mikegoelzer/Homebrew-ECP5-SBC/hardware/parts/GRM1885C1H121JA01D/G-188_MUR.step

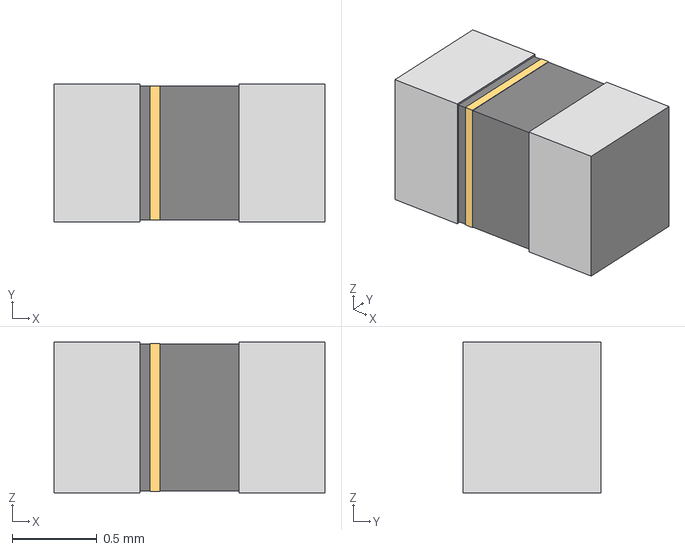
[picture p17: CAD file, 2024-12-17]
hardware/parts/GRM1885C1H121JA01D/G-188_MUR.step
1.60 x 0.812 x 0.889 mm
