mikegoelzer/Homebrew-ECP5-SBC/hardware/parts/ICD15S13E4GX00LF/ICD15S13E4GX00LF.step

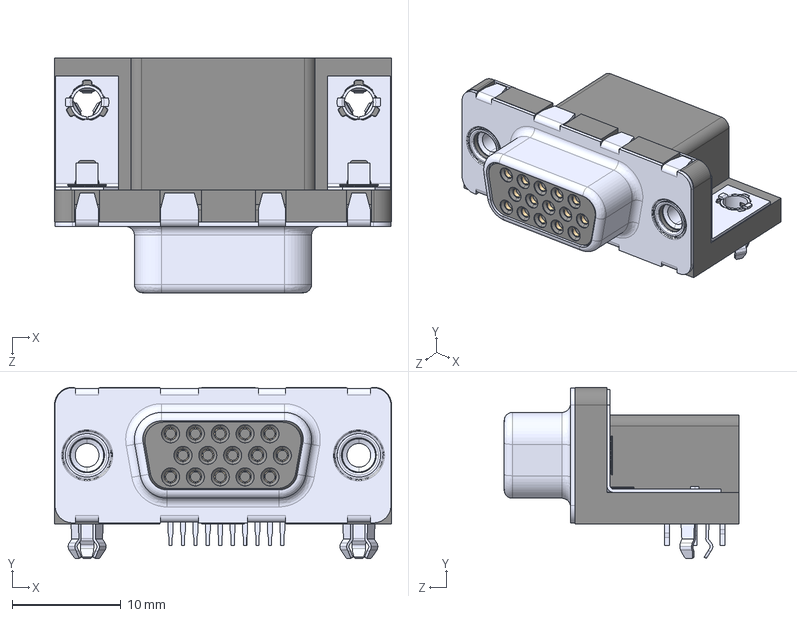
[picture p18: CAD file, 2025-01-06]
hardware/parts/ICD15S13E4GX00LF/ICD15S13E4GX00LF.step
31.0 x 15.7 x 21.6 mm
