mikegoelzer/Homebrew-ECP5-SBC/hardware/parts/IHLP1212ABERR47M11/IND_IHLP-1212AB_VIS.step

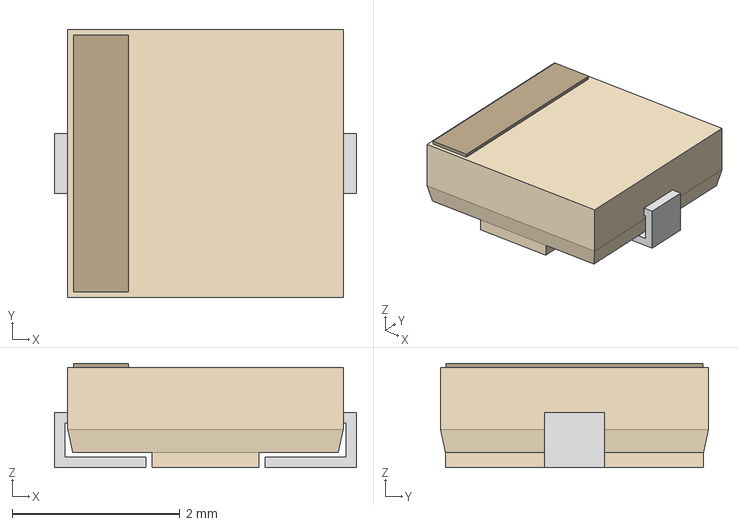
[picture p19: CAD file, 2024-12-17]
hardware/parts/IHLP1212ABERR47M11/IND_IHLP-1212AB_VIS.step
3.61 x 3.20 x 1.25 mm
