mikegoelzer/Homebrew-ECP5-SBC/hardware/parts/IHLP1212AEERR47M11/IND_IHLP-1212AE_VIS.step

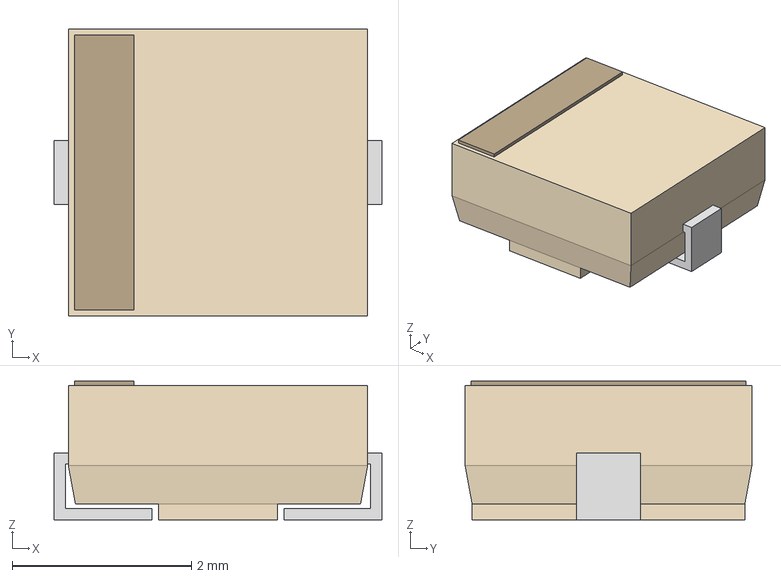
[picture p20: CAD file, 2024-12-17]
hardware/parts/IHLP1212AEERR47M11/IND_IHLP-1212AE_VIS.step
3.66 x 3.20 x 1.55 mm
