mikegoelzer/Homebrew-ECP5-SBC/hardware/parts/IHLP3232DZER2R2M11/IHLP3232DZ.step

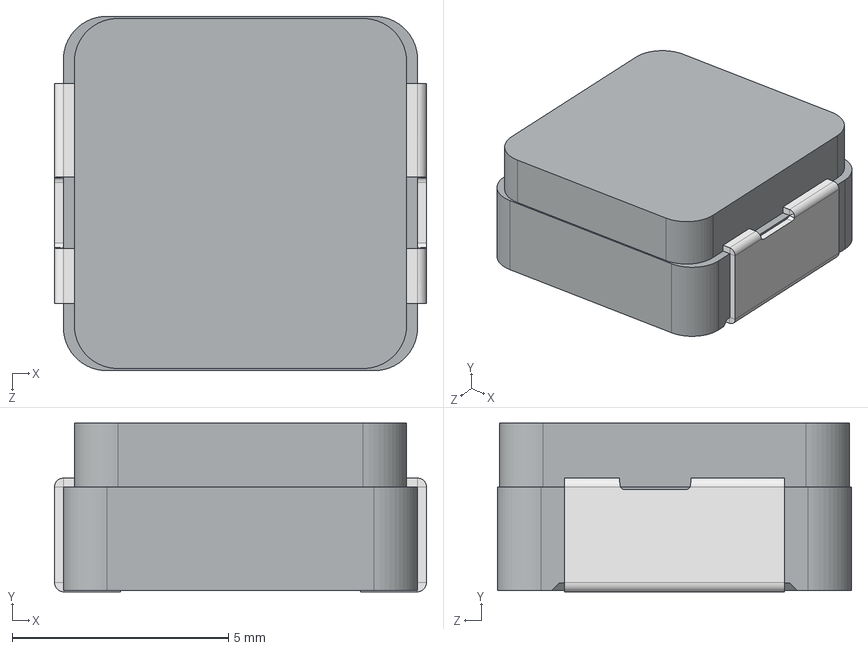
[picture p21: CAD file, 2024-12-17]
hardware/parts/IHLP3232DZER2R2M11/IHLP3232DZ.step
8.60 x 3.90 x 8.19 mm
