mikegoelzer/Homebrew-ECP5-SBC/hardware/parts/IHLP6767DZER6R8M11/IHLP6767DZ.step

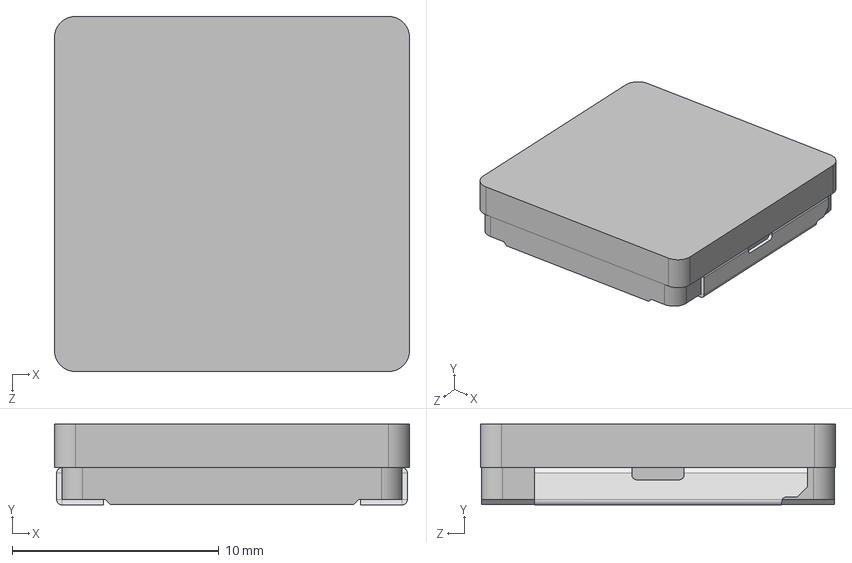
[picture p22: CAD file, 2025-01-10]
hardware/parts/IHLP6767DZER6R8M11/IHLP6767DZ.step
17.2 x 3.91 x 17.2 mm
