mikegoelzer/Homebrew-ECP5-SBC/hardware/parts/INA210BIDCKR/INA210BIDCKR.step

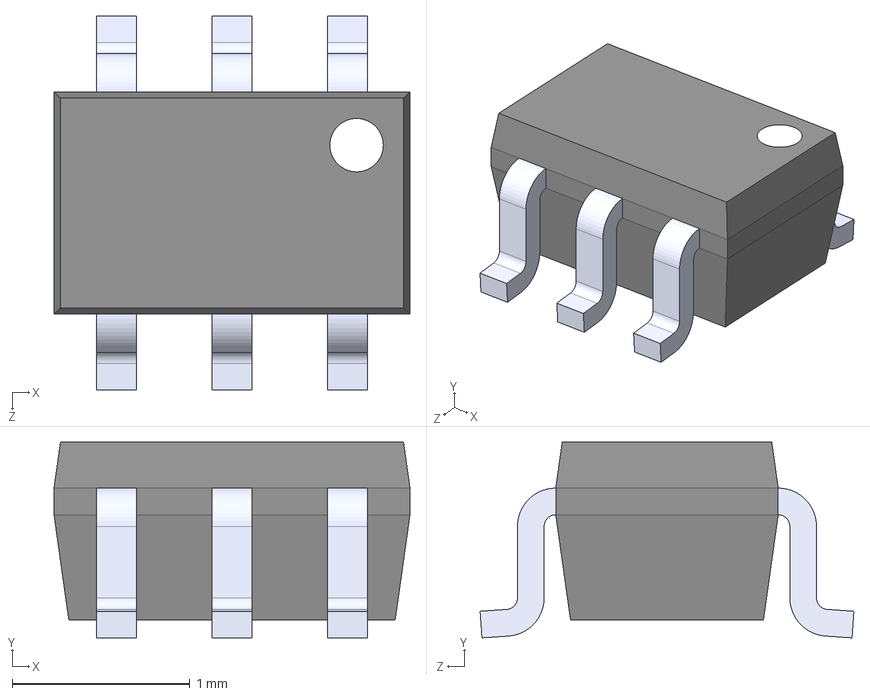
[picture p23: CAD file, 2024-12-17]
hardware/parts/INA210BIDCKR/INA210BIDCKR.step
2.00 x 1.10 x 2.10 mm
