mikegoelzer/Homebrew-ECP5-SBC/hardware/parts/IRF9540NSTRLPBF/IRF9540NSTRLPBF.step

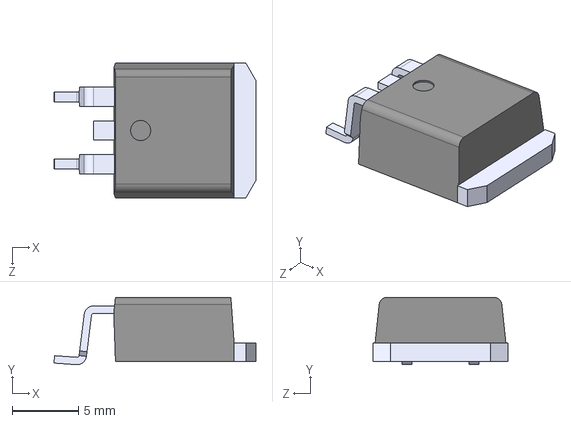
[picture p24: CAD file, 2024-12-17]
hardware/parts/IRF9540NSTRLPBF/IRF9540NSTRLPBF.step
15.2 x 5.08 x 10.2 mm
