mikegoelzer/Homebrew-ECP5-SBC/hardware/parts/Keystone_Testpoints/TestPointKeystone5002WHITE.step

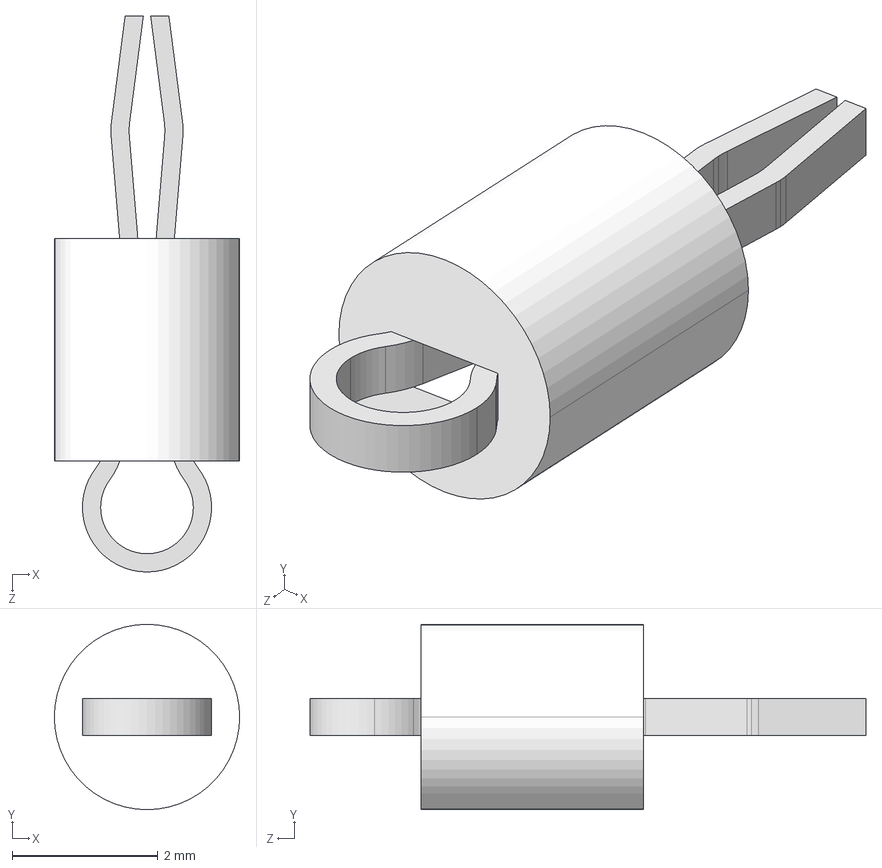
[picture p25: CAD file, 2025-01-06]
hardware/parts/Keystone_Testpoints/TestPointKeystone5002WHITE.step
2.54 x 2.54 x 7.62 mm
User Library-Test Point Keystone - 5002 WHITE_1
User Library-Test Point Keystone - 5002 WHITE_2
