mikegoelzer/Homebrew-ECP5-SBC/hardware/parts/LP2950CDTX_3_3_NOPB/NDP0003B.stp

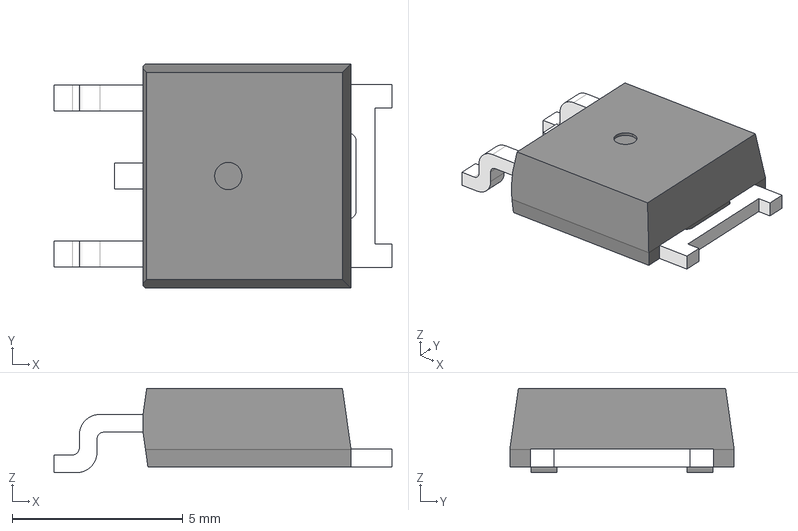
[picture p26: CAD file, 2025-01-10]
hardware/parts/LP2950CDTX_3_3_NOPB/NDP0003B.stp
9.91 x 6.58 x 2.47 mm
BODY_NDP0003B
HSINK_NDP0003B
LEAD_NDP0003B x 2
CLEAD_NDP0003B
