mikegoelzer/Homebrew-ECP5-SBC/hardware/parts/MSD_4_A/MSD-4-A.step

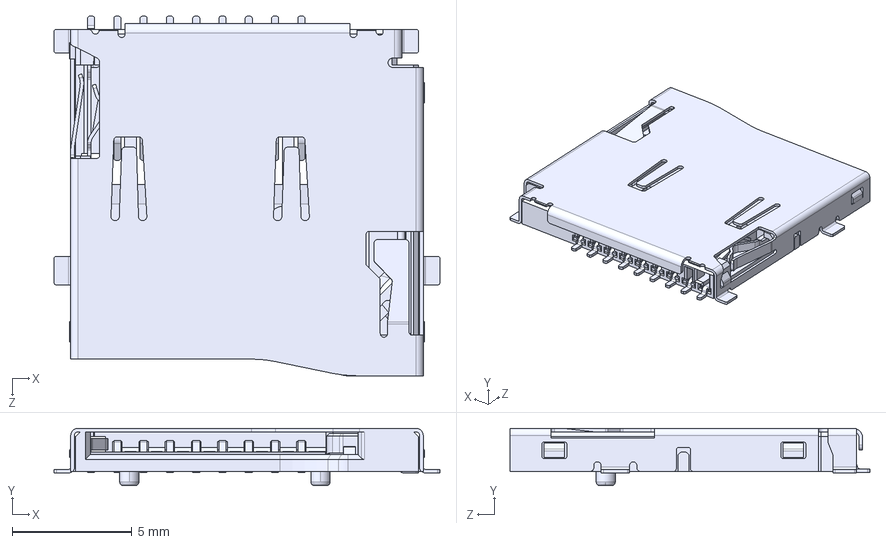
[picture p27: CAD file, 2025-01-15]
hardware/parts/MSD_4_A/MSD-4-A.step
16.1 x 2.40 x 15.0 mm
