mikegoelzer/Homebrew-ECP5-SBC/hardware/parts/PCV1V560MCL1GS/KiCADv6/PCV1V560MCL1GS.step

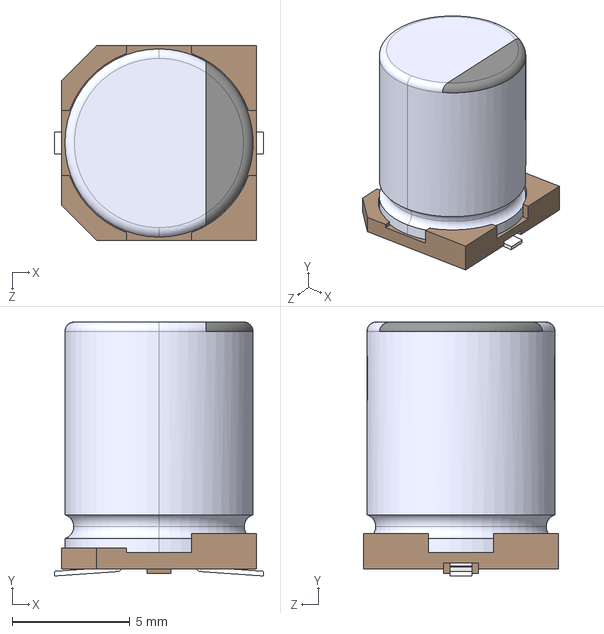
[picture p28: CAD file, 2024-12-17]
hardware/parts/PCV1V560MCL1GS/KiCADv6/PCV1V560MCL1GS.step
8.90 x 10.8 x 8.30 mm
