mikegoelzer/Homebrew-ECP5-SBC/hardware/parts/PH1-03-UA/PH1-03-UA.STEP

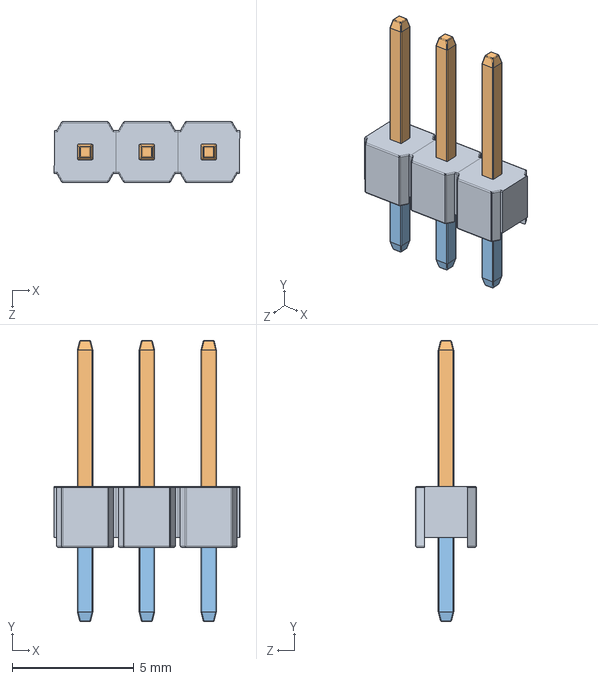
[picture p29: CAD file, 2025-01-06]
hardware/parts/PH1-03-UA/PH1-03-UA.STEP
7.63 x 11.6 x 2.50 mm
