mikegoelzer/Homebrew-ECP5-SBC/hardware/parts/PH1RB-02-UA/PH1RB-02-UA.STEP

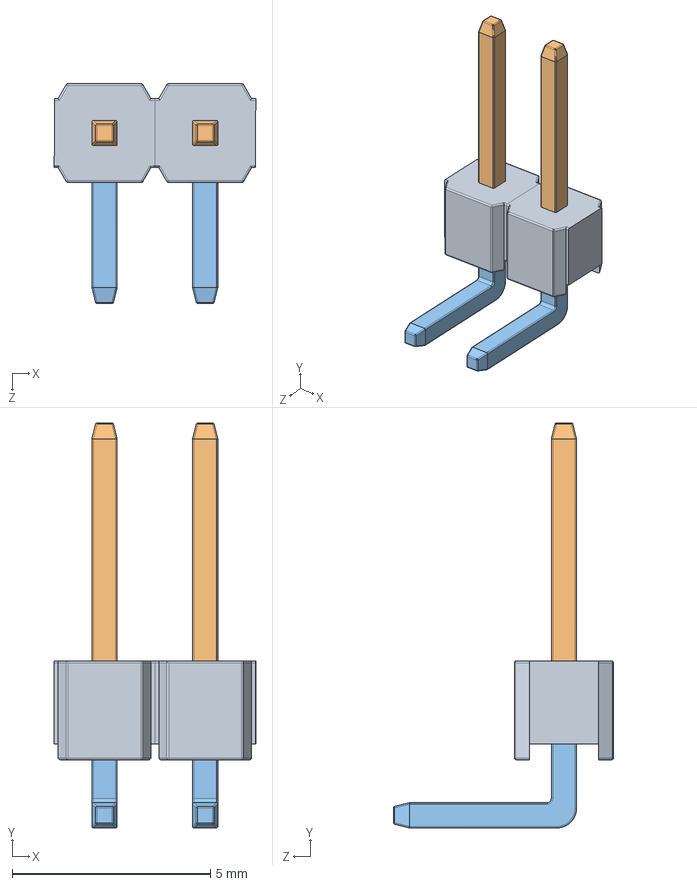
[picture p30: CAD file, 2025-01-06]
hardware/parts/PH1RB-02-UA/PH1RB-02-UA.STEP
5.09 x 10.2 x 5.55 mm
