mikegoelzer/Homebrew-ECP5-SBC/hardware/parts/PH2_06_UA/CONN_PH2-06-UA_ADM.step

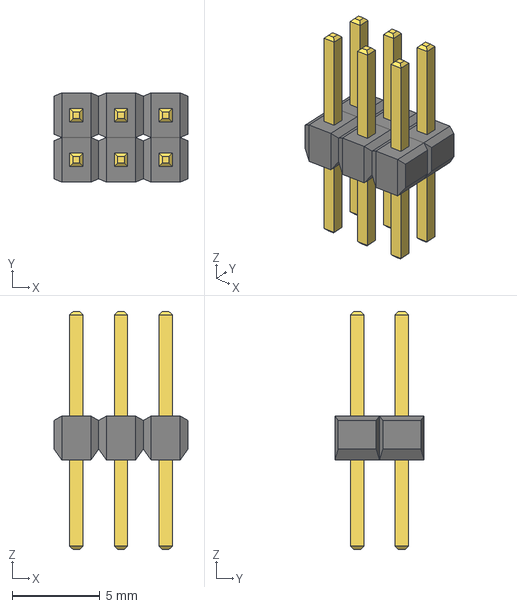
[picture p31: CAD file, 2025-01-06]
hardware/parts/PH2_06_UA/CONN_PH2-06-UA_ADM.step
7.62 x 5.08 x 13.5 mm
