mikegoelzer/Homebrew-ECP5-SBC/hardware/parts/PH2RA-08-UA/PH2RA-08-UA.STEP

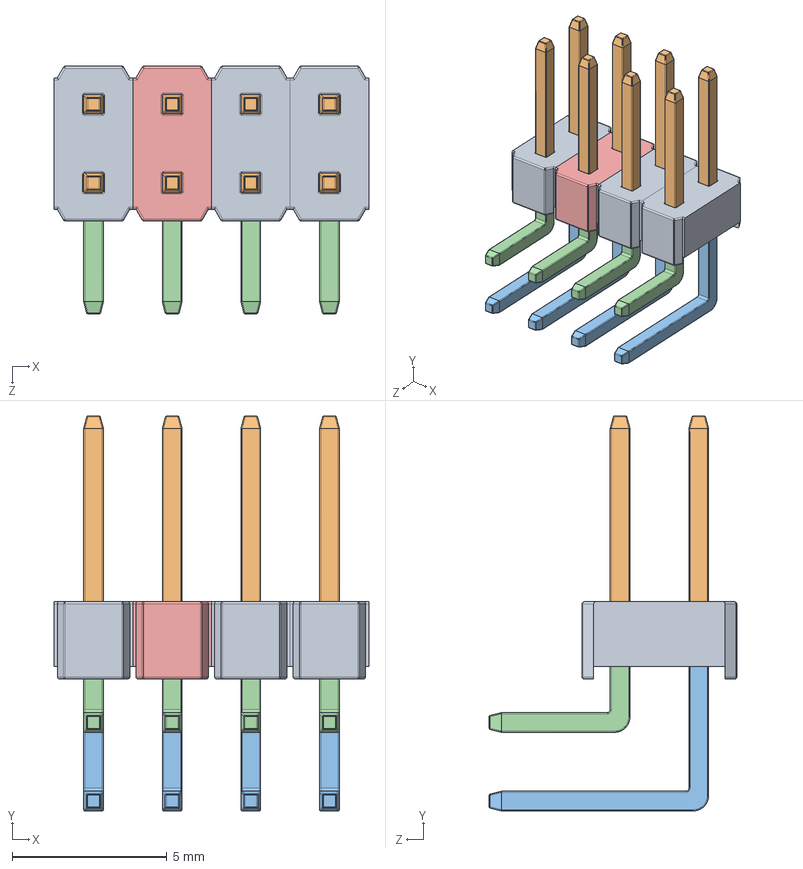
[picture p32: CAD file, 2025-01-06]
hardware/parts/PH2RA-08-UA/PH2RA-08-UA.STEP
10.2 x 12.8 x 8.00 mm
