mikegoelzer/Homebrew-ECP5-SBC/hardware/parts/pmod-ports/PH1RB-06-UA.STEP

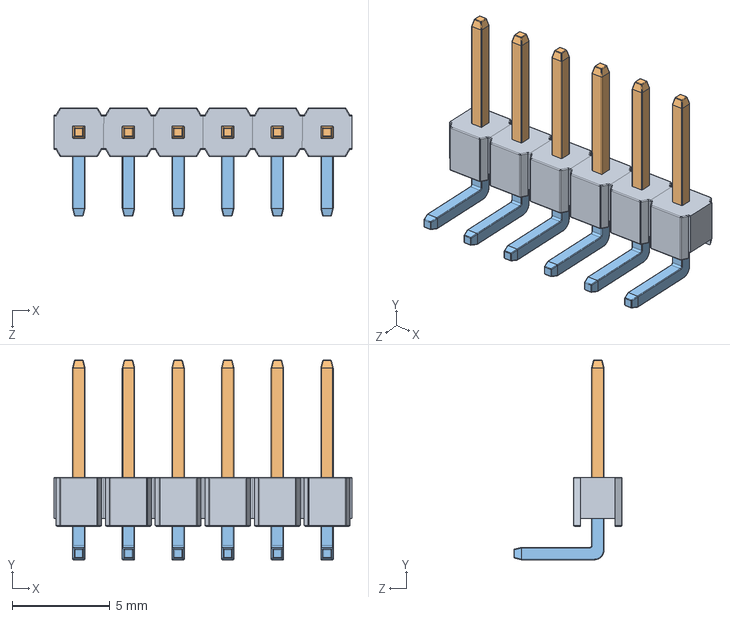
[picture p33: CAD file, 2025-01-06]
hardware/parts/pmod-ports/PH1RB-06-UA.STEP
15.2 x 10.2 x 5.55 mm
