mikegoelzer/Homebrew-ECP5-SBC/hardware/parts/PPPC082LFBN-RC/PPPC082LFBN-RC.STEP

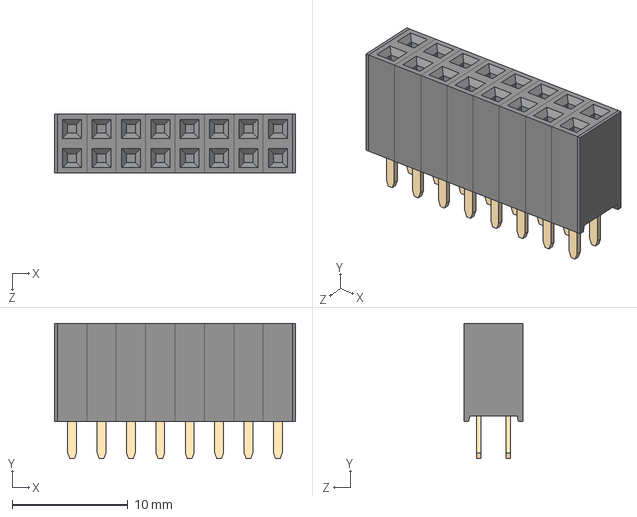
[picture p34: CAD file, 2025-01-10]
hardware/parts/PPPC082LFBN-RC/PPPC082LFBN-RC.STEP
20.8 x 11.7 x 5.08 mm
NPPC202LFBN-RC_C08
Pin - Gold x 8
