mikegoelzer/Homebrew-ECP5-SBC/hardware/parts/PPPC201LFBN/PPPC201LFBN-RC.STEP

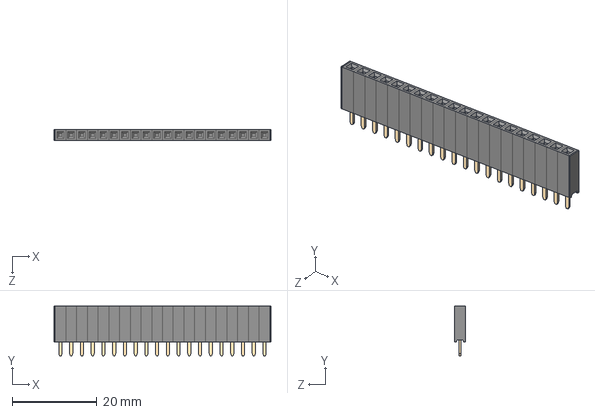
[picture p35: CAD file, 2025-01-15]
hardware/parts/PPPC201LFBN/PPPC201LFBN-RC.STEP
51.3 x 11.7 x 2.54 mm
PPPC021LFBN-RC_C20
Pin - Gold x 20
