mikegoelzer/Homebrew-ECP5-SBC/hardware/parts/PPTC062LFBN/PPTC062LFBN-RC.STEP

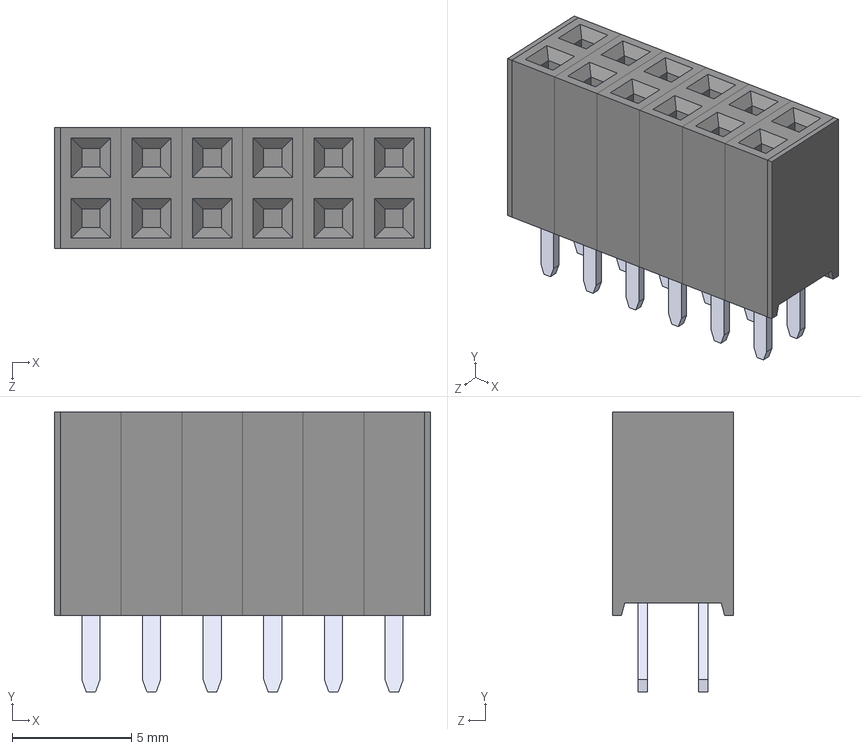
[picture p36: CAD file, 2025-01-15]
hardware/parts/PPTC062LFBN/PPTC062LFBN-RC.STEP
15.7 x 11.7 x 5.08 mm
NPPC202LFBN-RC_C06
Pin - Tin x 6
