mikegoelzer/Homebrew-ECP5-SBC/hardware/parts/PPTC071LFBN/PPTC071LFBN-RC.STEP

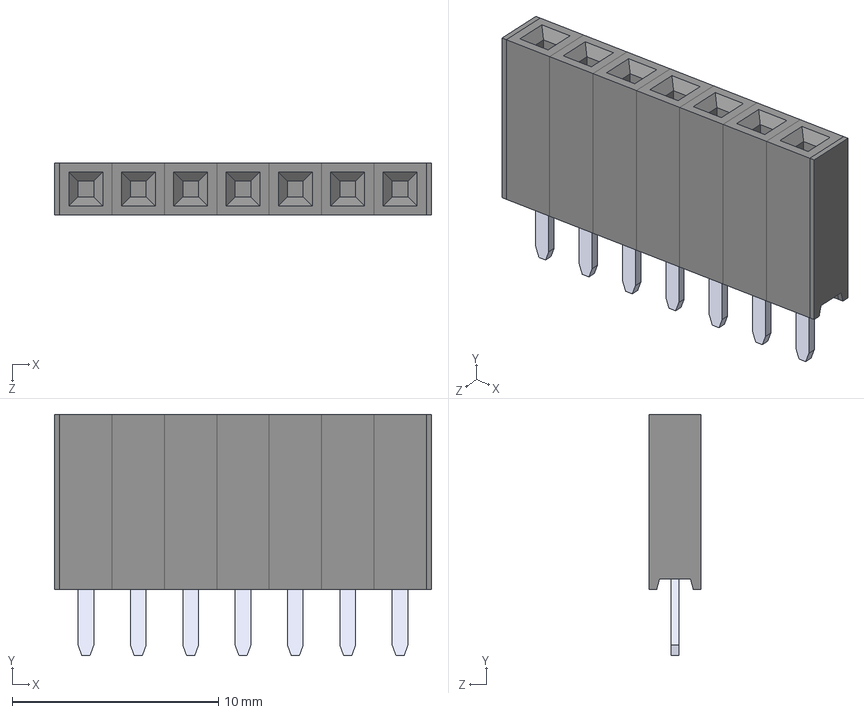
[picture p37: CAD file, 2025-01-15]
hardware/parts/PPTC071LFBN/PPTC071LFBN-RC.STEP
18.3 x 11.7 x 2.54 mm
PPPC021LFBN-RC_C07
Pin - Tin x 7
