mikegoelzer/Homebrew-ECP5-SBC/hardware/parts/PTS645SL50SMTR92LFS/PTS645SL50SMTR92LFS/3D/PTS645SL50SMTR92LFS.stp

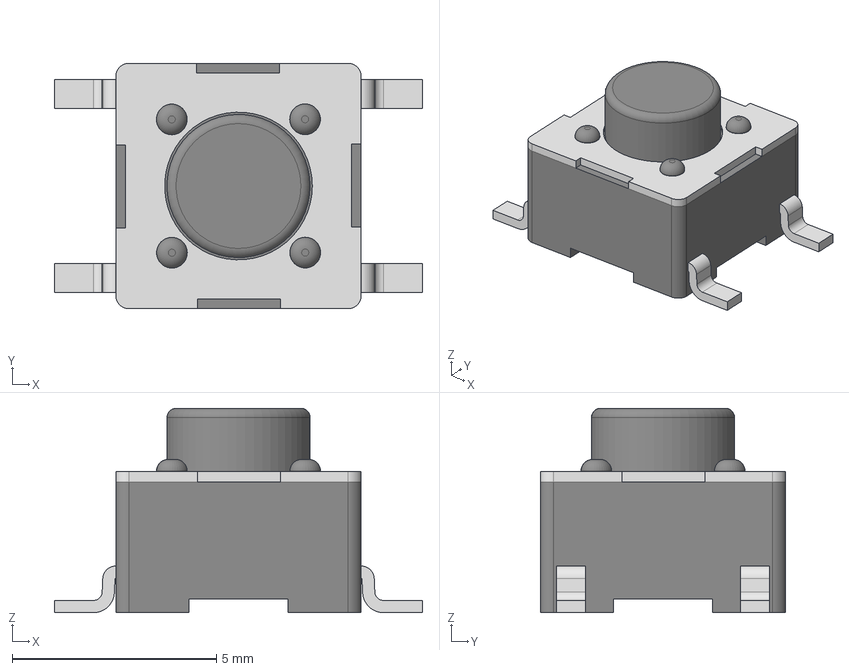
[picture p38: CAD file, 2025-01-06]
hardware/parts/PTS645SL50SMTR92LFS/PTS645SL50SMTR92LFS/3D/PTS645SL50SMTR92LFS.stp
9.00 x 6.00 x 5.00 mm
