mikegoelzer/Homebrew-ECP5-SBC/hardware/parts/QBLP631_IW/QBLP631_MONO.step

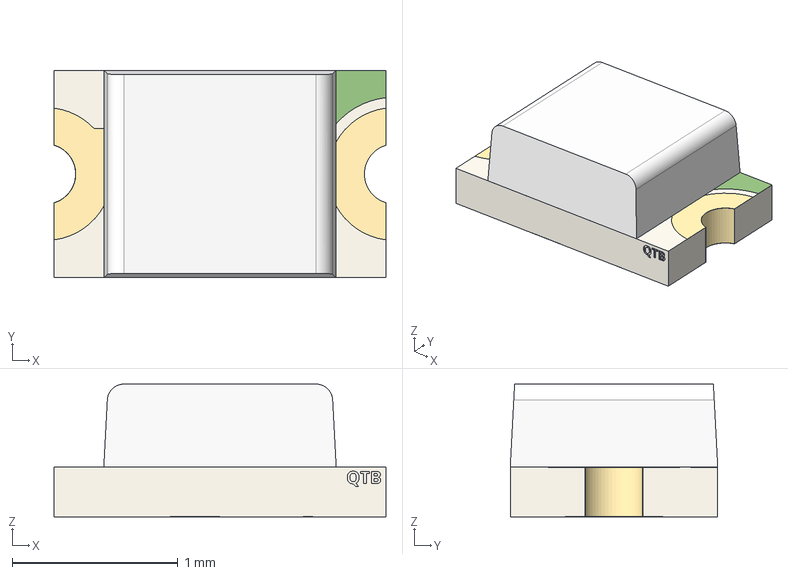
[picture p39: CAD file, 2025-01-06]
hardware/parts/QBLP631_IW/QBLP631_MONO.step
2.00 x 1.25 x 0.8 mm
Resin
Polarity Mark
Bottom Pad 2
Bottom Pad 1
Bottom Pad - Mid
