mikegoelzer/Homebrew-ECP5-SBC/hardware/parts/TFP401PZP/PZP0100H.stp

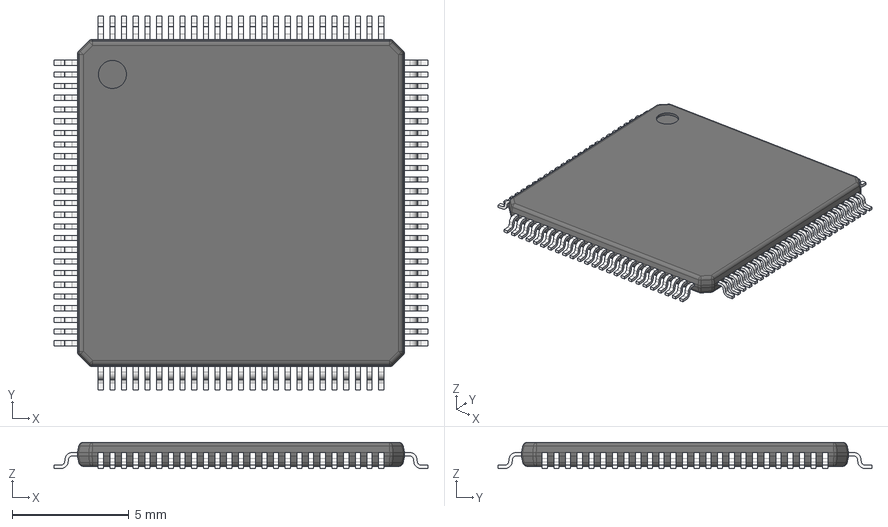
[picture p40: CAD file, 2025-01-06]
hardware/parts/TFP401PZP/PZP0100H.stp
16.0 x 16.0 x 1.12 mm
LEAD-QFP x 100
THERMAL_PAD
