mikegoelzer/Homebrew-ECP5-SBC/hardware/parts/TMUX1574PWR/TMUX1574PWR.step

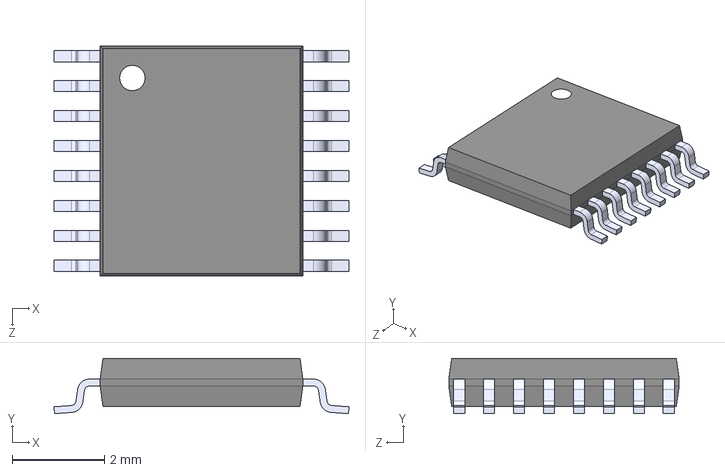
[picture p41: CAD file, 2025-01-06]
hardware/parts/TMUX1574PWR/TMUX1574PWR.step
6.40 x 1.20 x 5.00 mm
