mikegoelzer/Homebrew-ECP5-SBC/hardware/parts/TPS552882RPMR/RPM0026A.stp

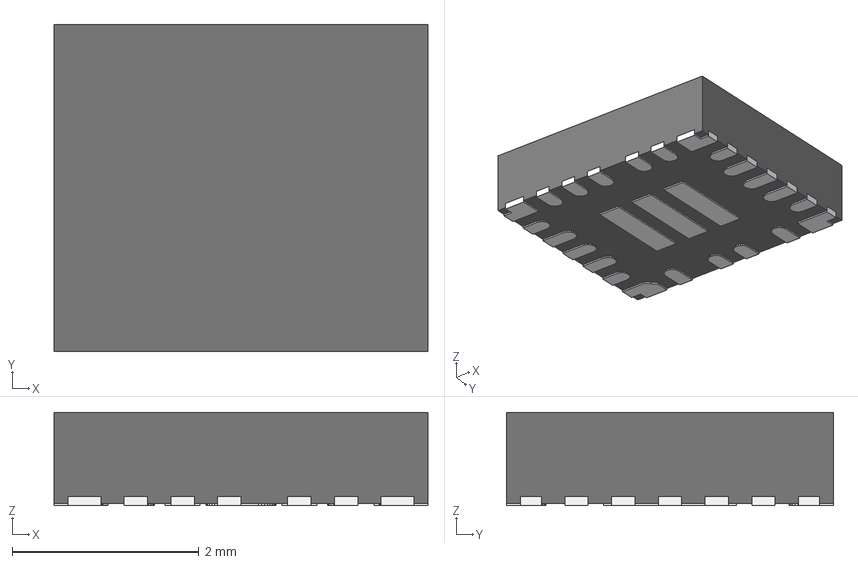
[picture p42: CAD file, 2025-01-10]
hardware/parts/TPS552882RPMR/RPM0026A.stp
4.00 x 3.50 x 1.00 mm
FRAME
MOLD
