mikegoelzer/Homebrew-ECP5-SBC/hardware/parts/USB4105_GF_A_120/USB4105-GF-A-120.step

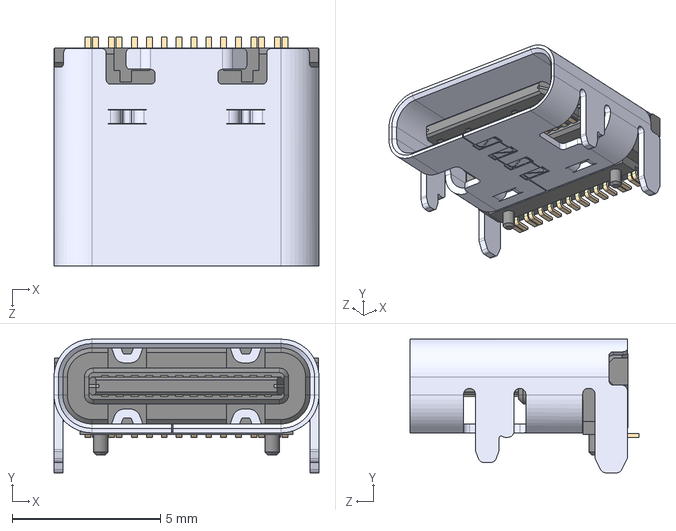
[picture p43: CAD file, 2025-01-06]
hardware/parts/USB4105_GF_A_120/USB4105-GF-A-120.step
8.94 x 4.51 x 7.71 mm
