mikegoelzer/Homebrew-ECP5-SBC/hardware/parts/USB4110_GF_A/USB4110GFA.step

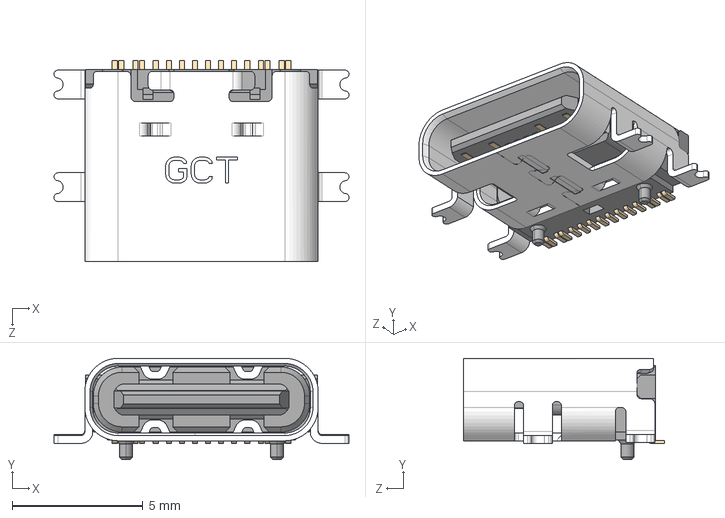
[picture p44: CAD file, 2024-12-23]
hardware/parts/USB4110_GF_A/USB4110GFA.step
11.3 x 3.89 x 7.70 mm
