mikegoelzer/Homebrew-ECP5-SBC/hardware/parts/W25Q128JVSIQ/W25Q128JVSIQ.step

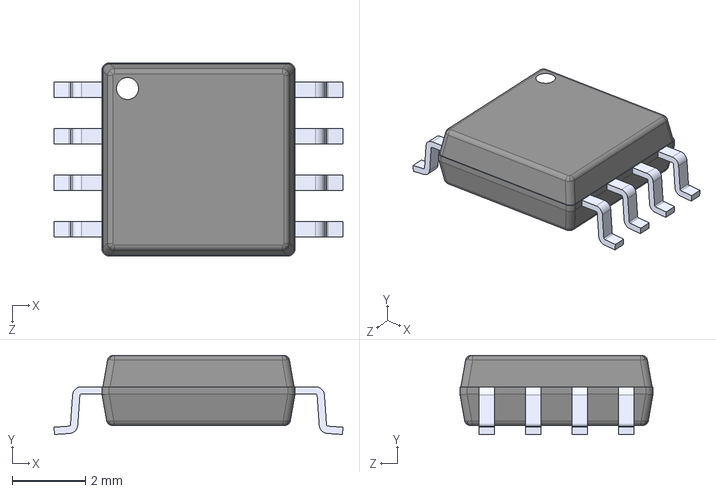
[picture p45: CAD file, 2024-12-17]
hardware/parts/W25Q128JVSIQ/W25Q128JVSIQ.step
7.90 x 2.16 x 5.28 mm
