mikegoelzer/Homebrew-ECP5-SBC/hardware/parts/Wurth-150080xS7500-Series-LEDs/Download_STP_WL-SMCW-0805_rev1.stp

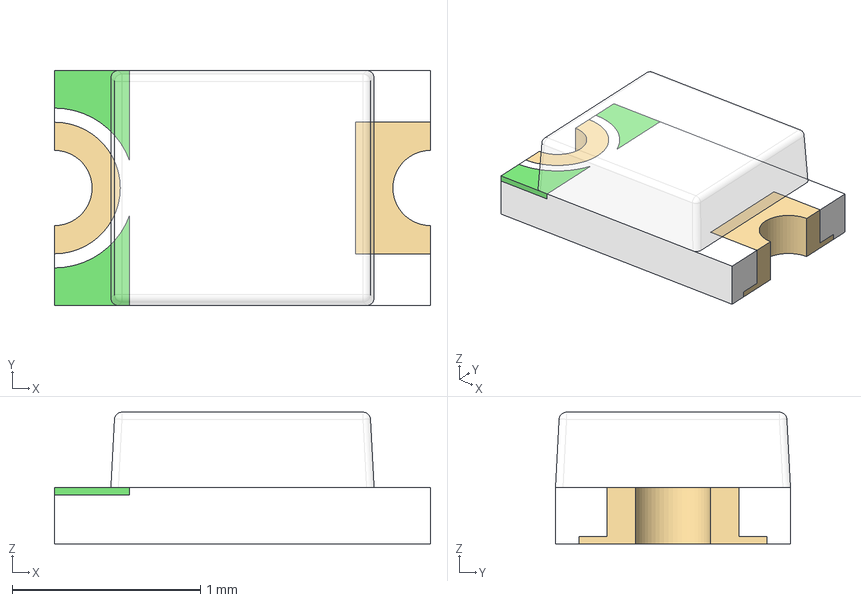
[picture p46: CAD file, 2025-01-06]
hardware/parts/Wurth-150080xS7500-Series-LEDs/Download_STP_WL-SMCW-0805_rev1.stp
2.00 x 1.25 x 0.7 mm
housing
marking x 2
cover
base_2
base
