mikegoelzer/Homebrew-ECP5-SBC/hardware/parts/pmod-ports/PH2RA-12-UA.STEP

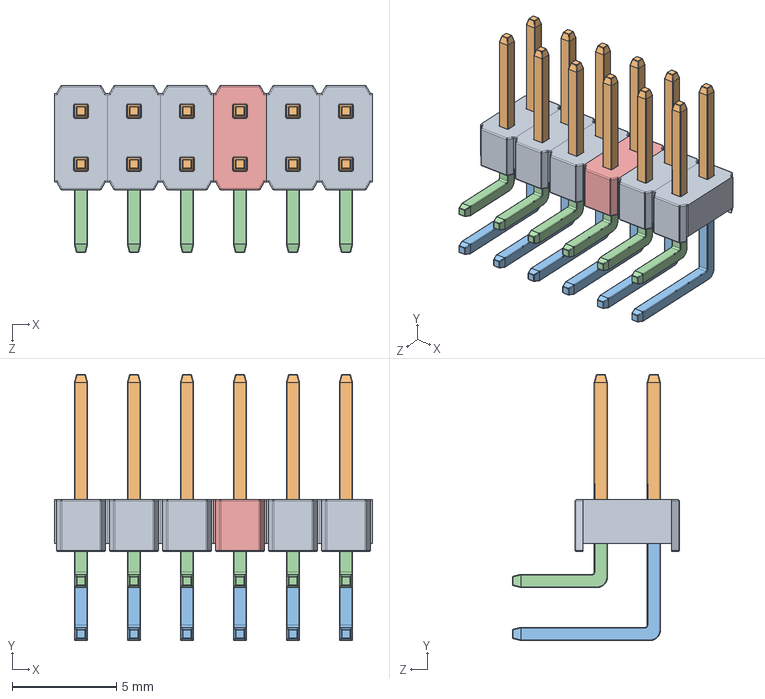
[picture p47: CAD file, 2025-01-06]
hardware/parts/pmod-ports/PH2RA-12-UA.STEP
15.2 x 12.8 x 8.00 mm
