mikegoelzer/Homebrew-ECP5-SBC/hardware/parts/xm/DF40HC3.5-20DS-0.4V_51.step

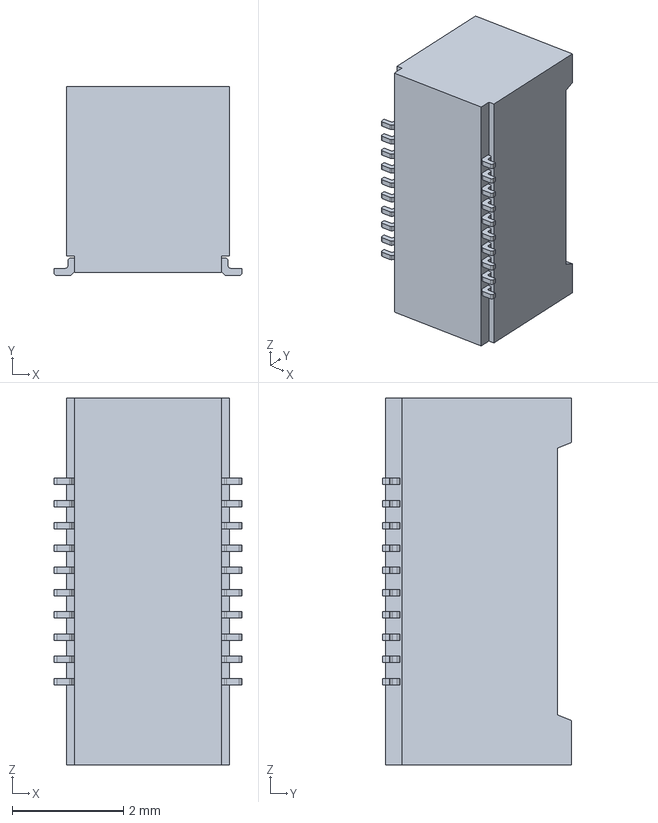
[picture p48: CAD file, 2025-01-06]
hardware/parts/xm/DF40HC3.5-20DS-0.4V_51.step
3.38 x 3.40 x 6.60 mm
