mikegoelzer/Homebrew-ECP5-SBC/hardware/parts/xm/DF40C-20DP.stp

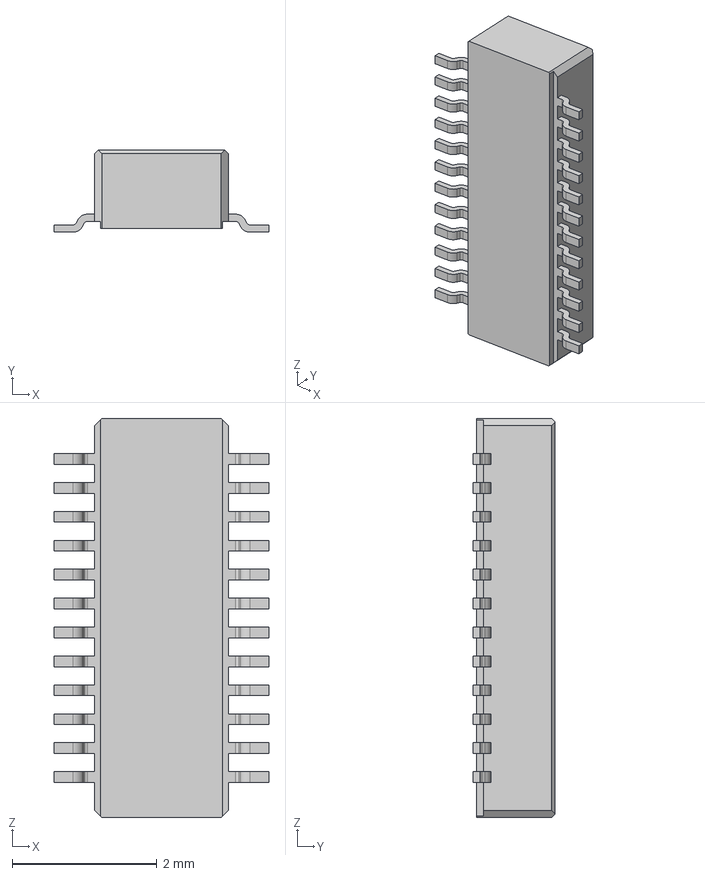
[picture p49: CAD file, 2025-01-06]
hardware/parts/xm/DF40C-20DP.stp
2.97 x 1.14 x 5.52 mm
